mentalDetector/Quansheng_UV-K5_PCB_R51-V1.4_PCB_Reversing_Rev._0.9/Quansheng_UV-K5_PCB_R51-V1.4.kicad_sch

## KiCad design Quansheng_UV-K5_PCB_R51-V1.4.kicad_sch (2024-04-22)

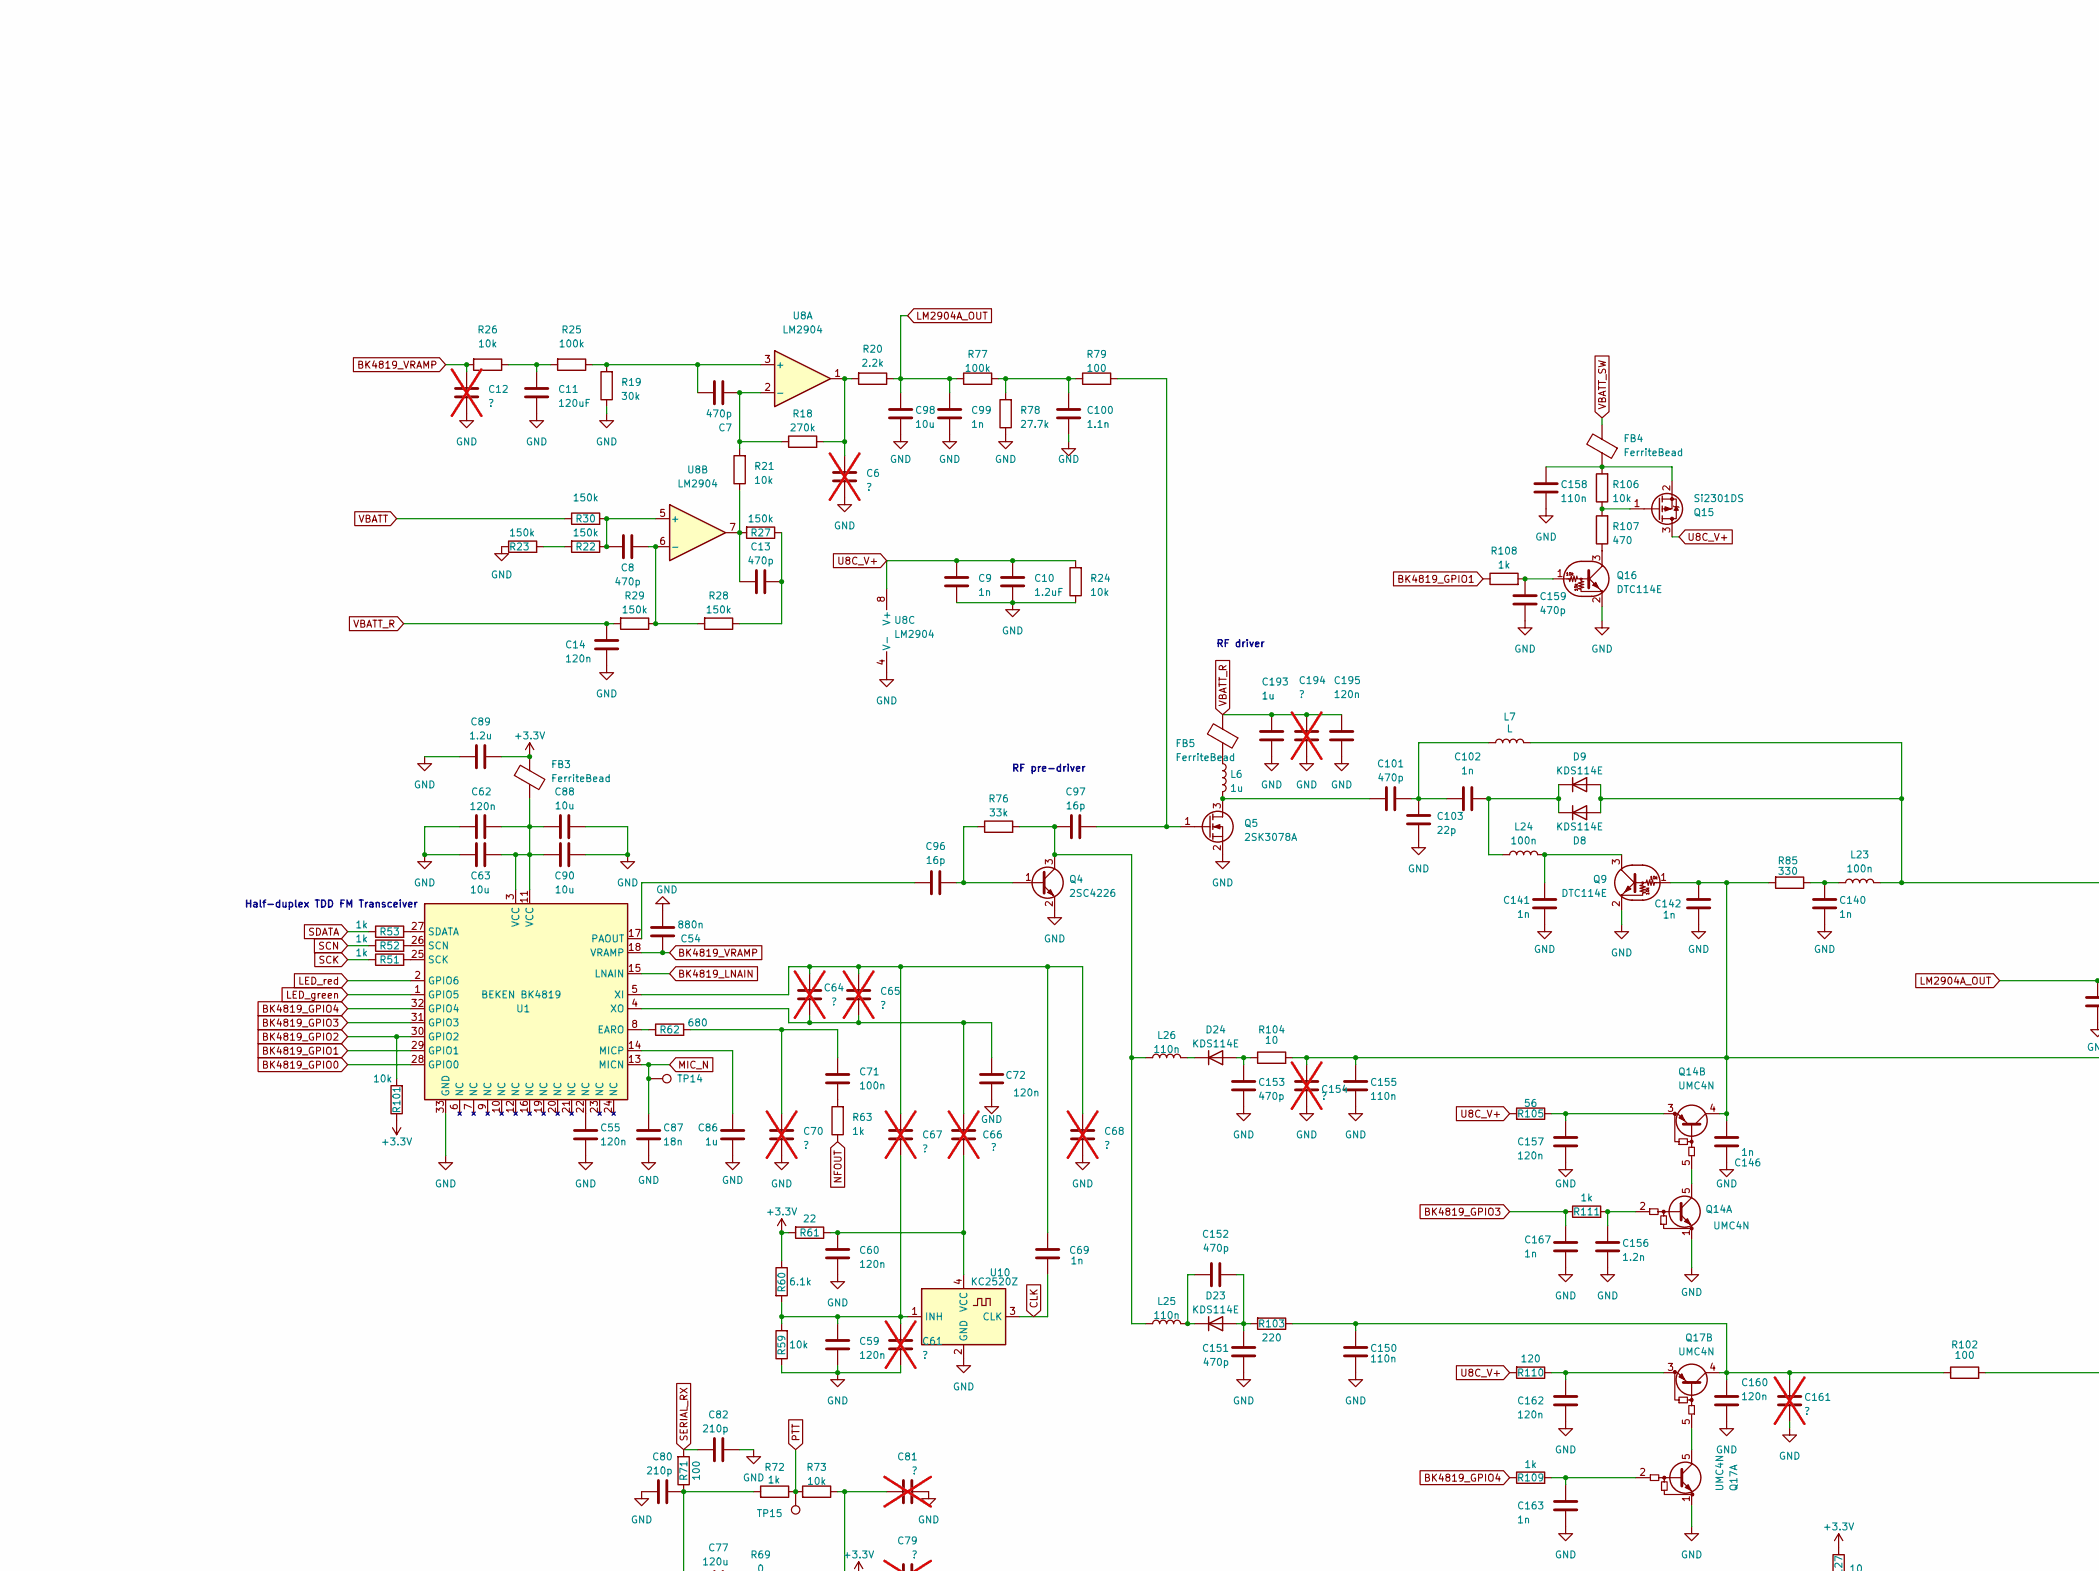
[picture p12: schematic Quansheng_UV-K5_PCB_R51-V1.4.kicad_sch, part in row 1, column 1]

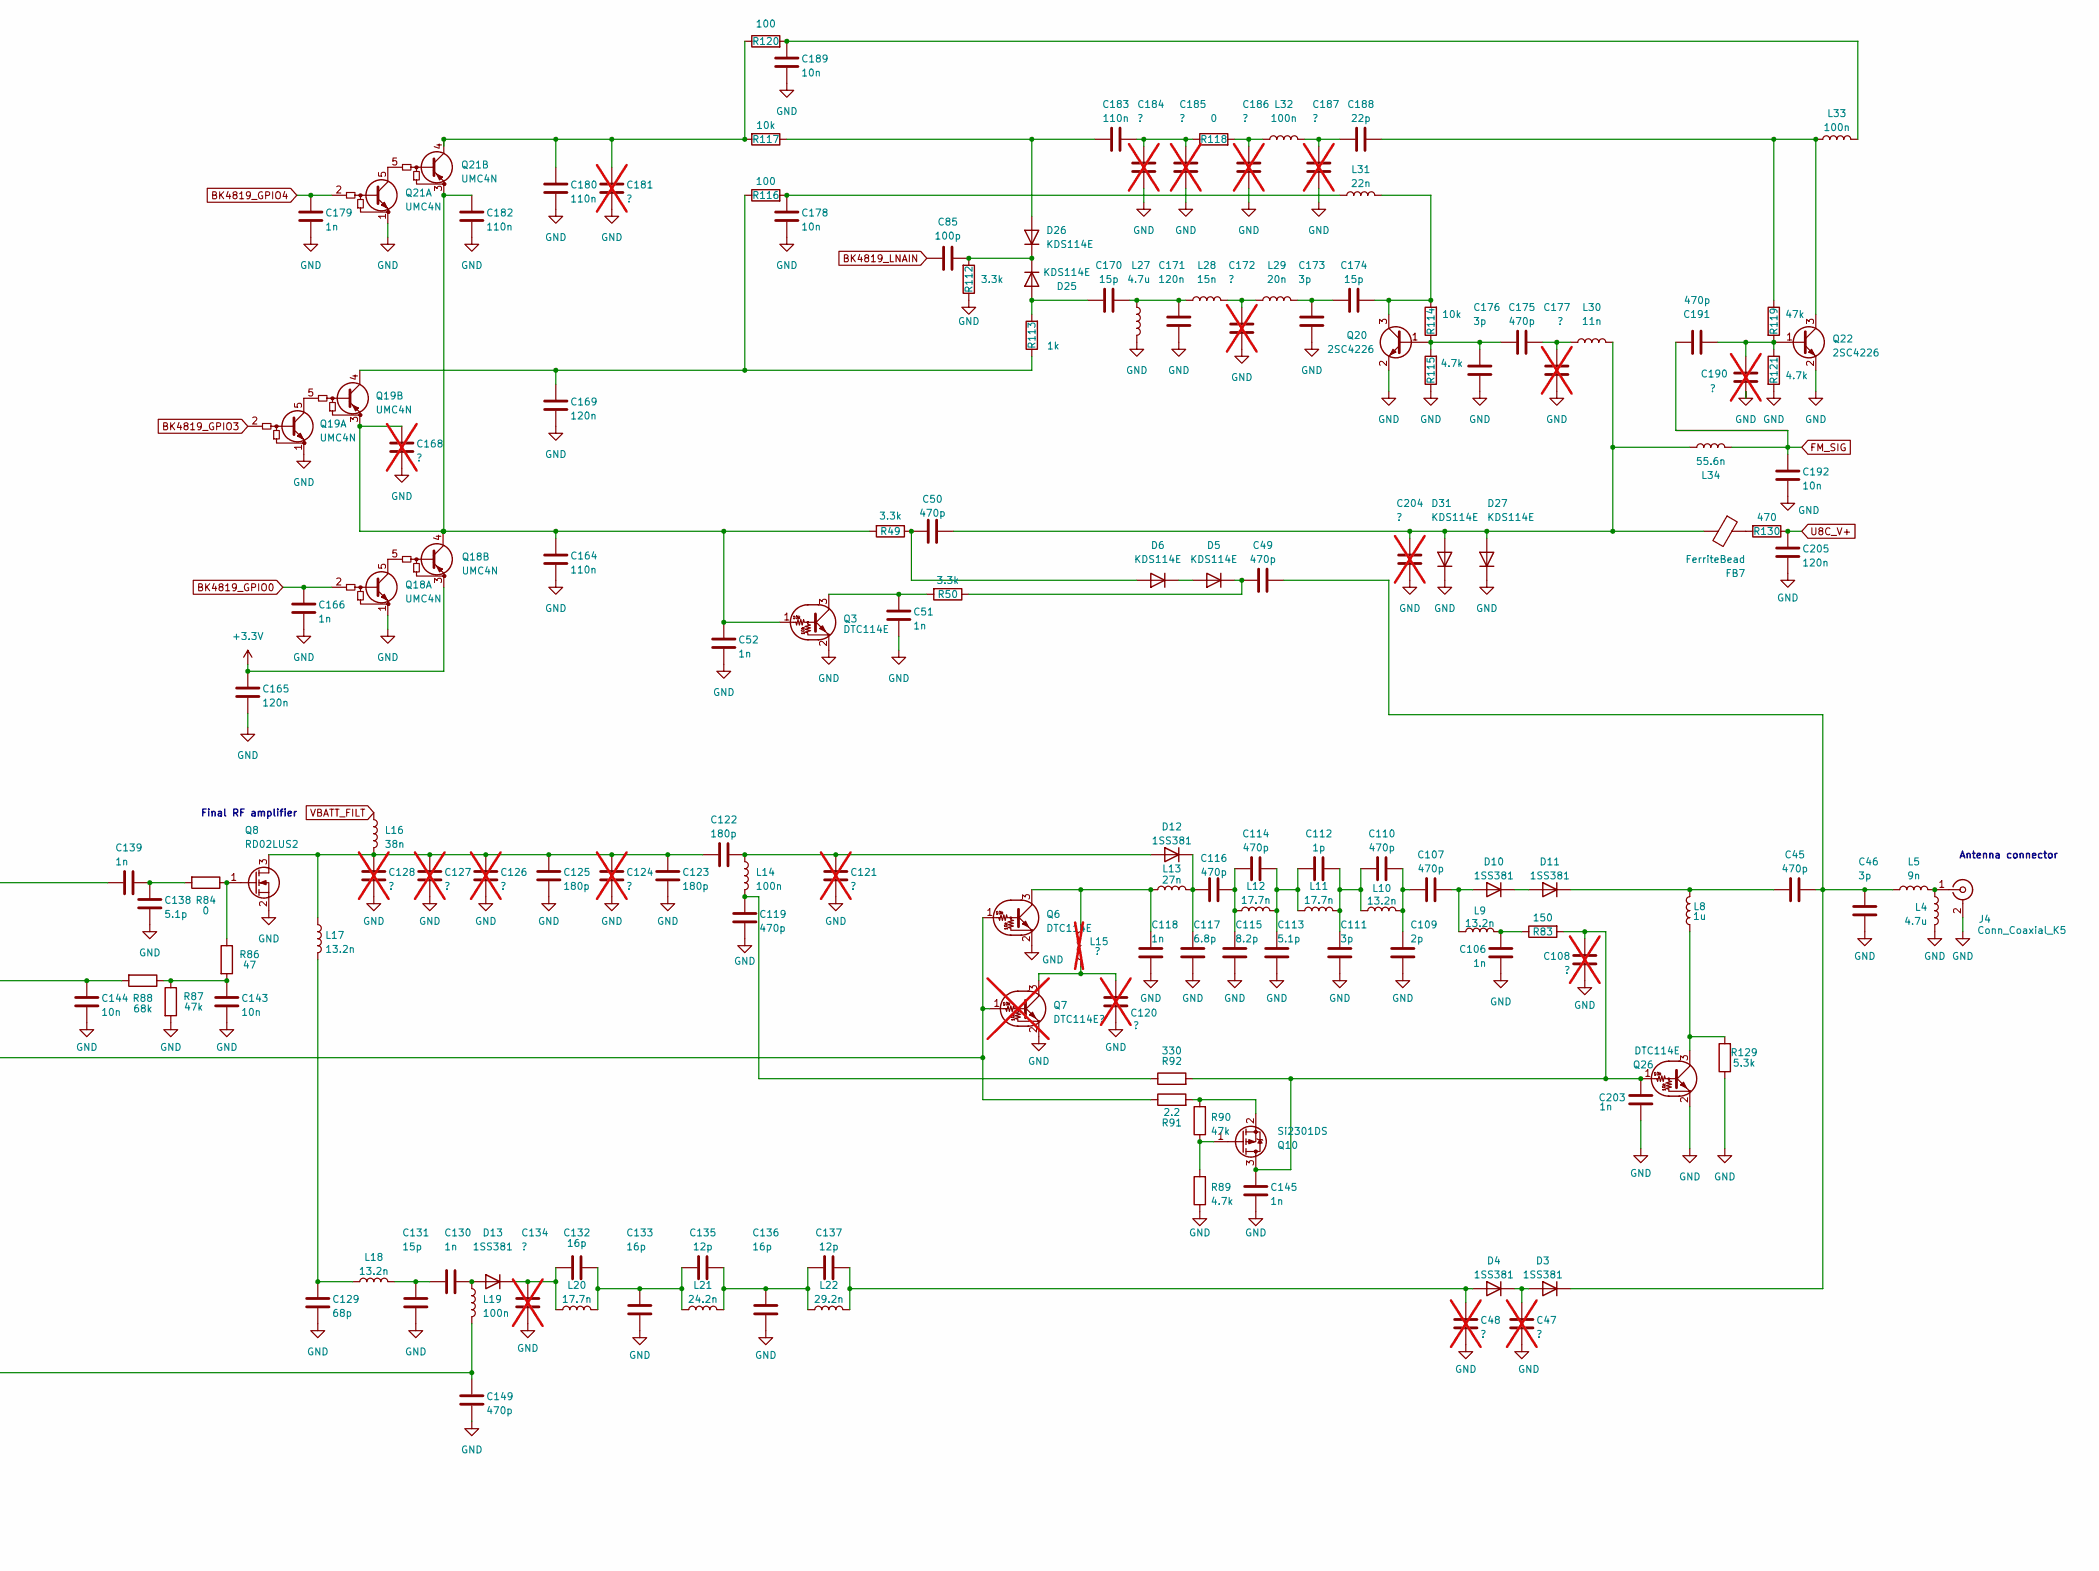
[picture p13: schematic Quansheng_UV-K5_PCB_R51-V1.4.kicad_sch, part in row 1, column 2]

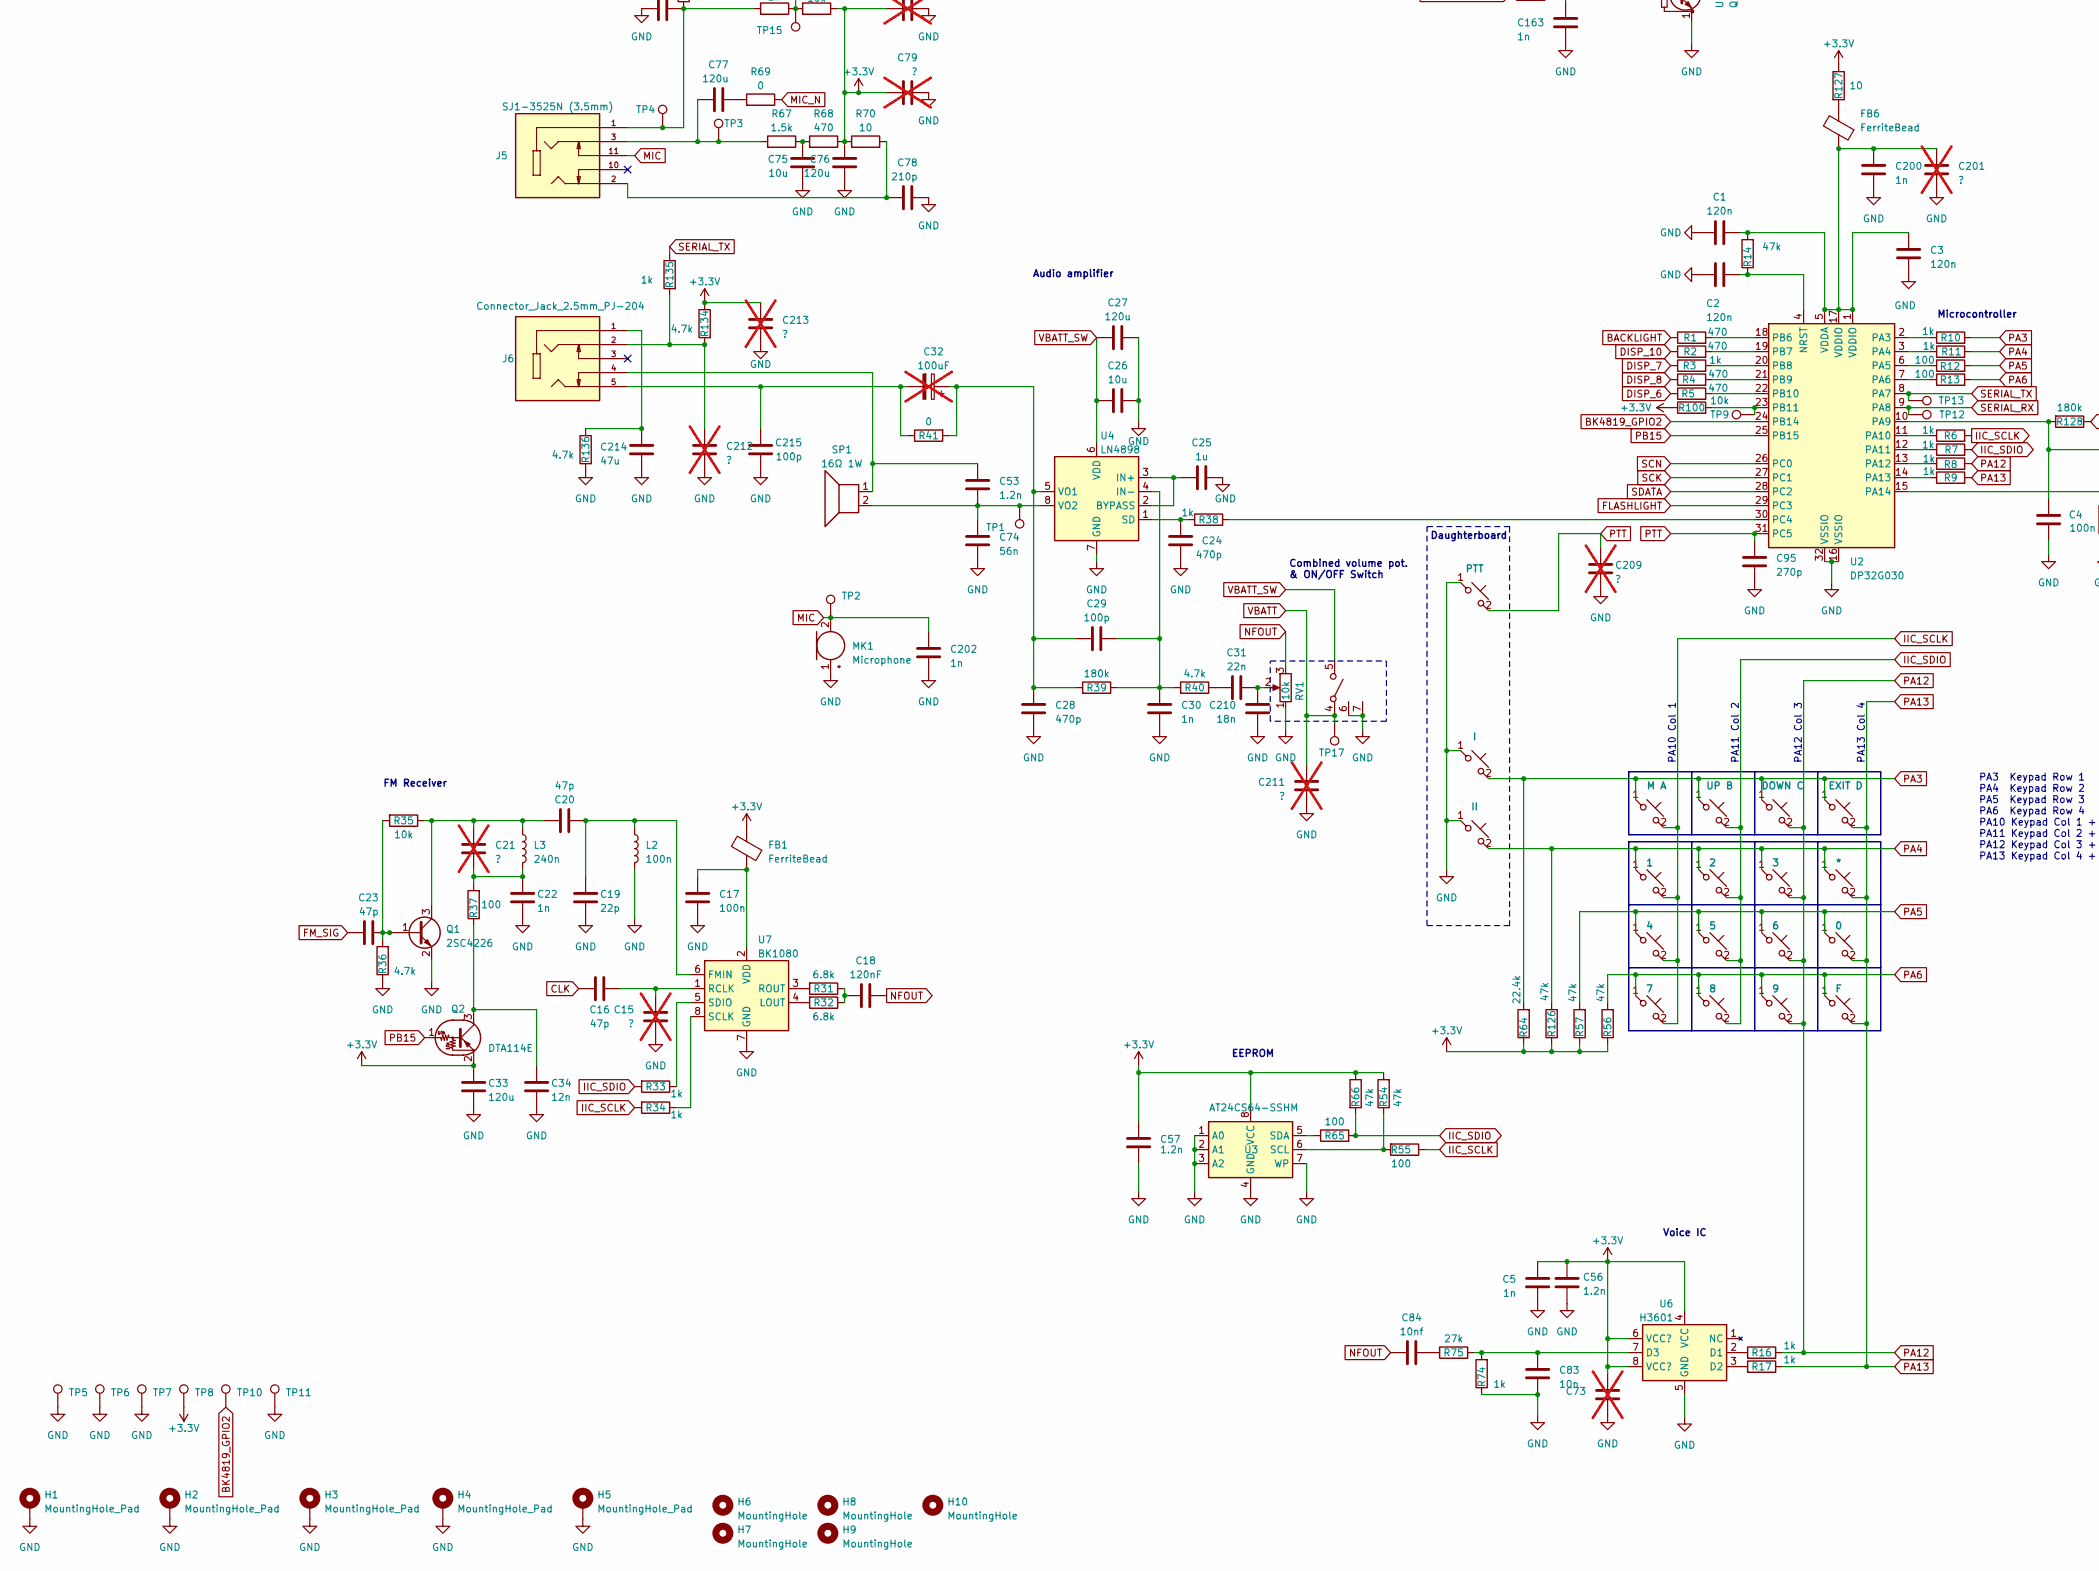
[picture p14: schematic Quansheng_UV-K5_PCB_R51-V1.4.kicad_sch, part in row 2, column 1]

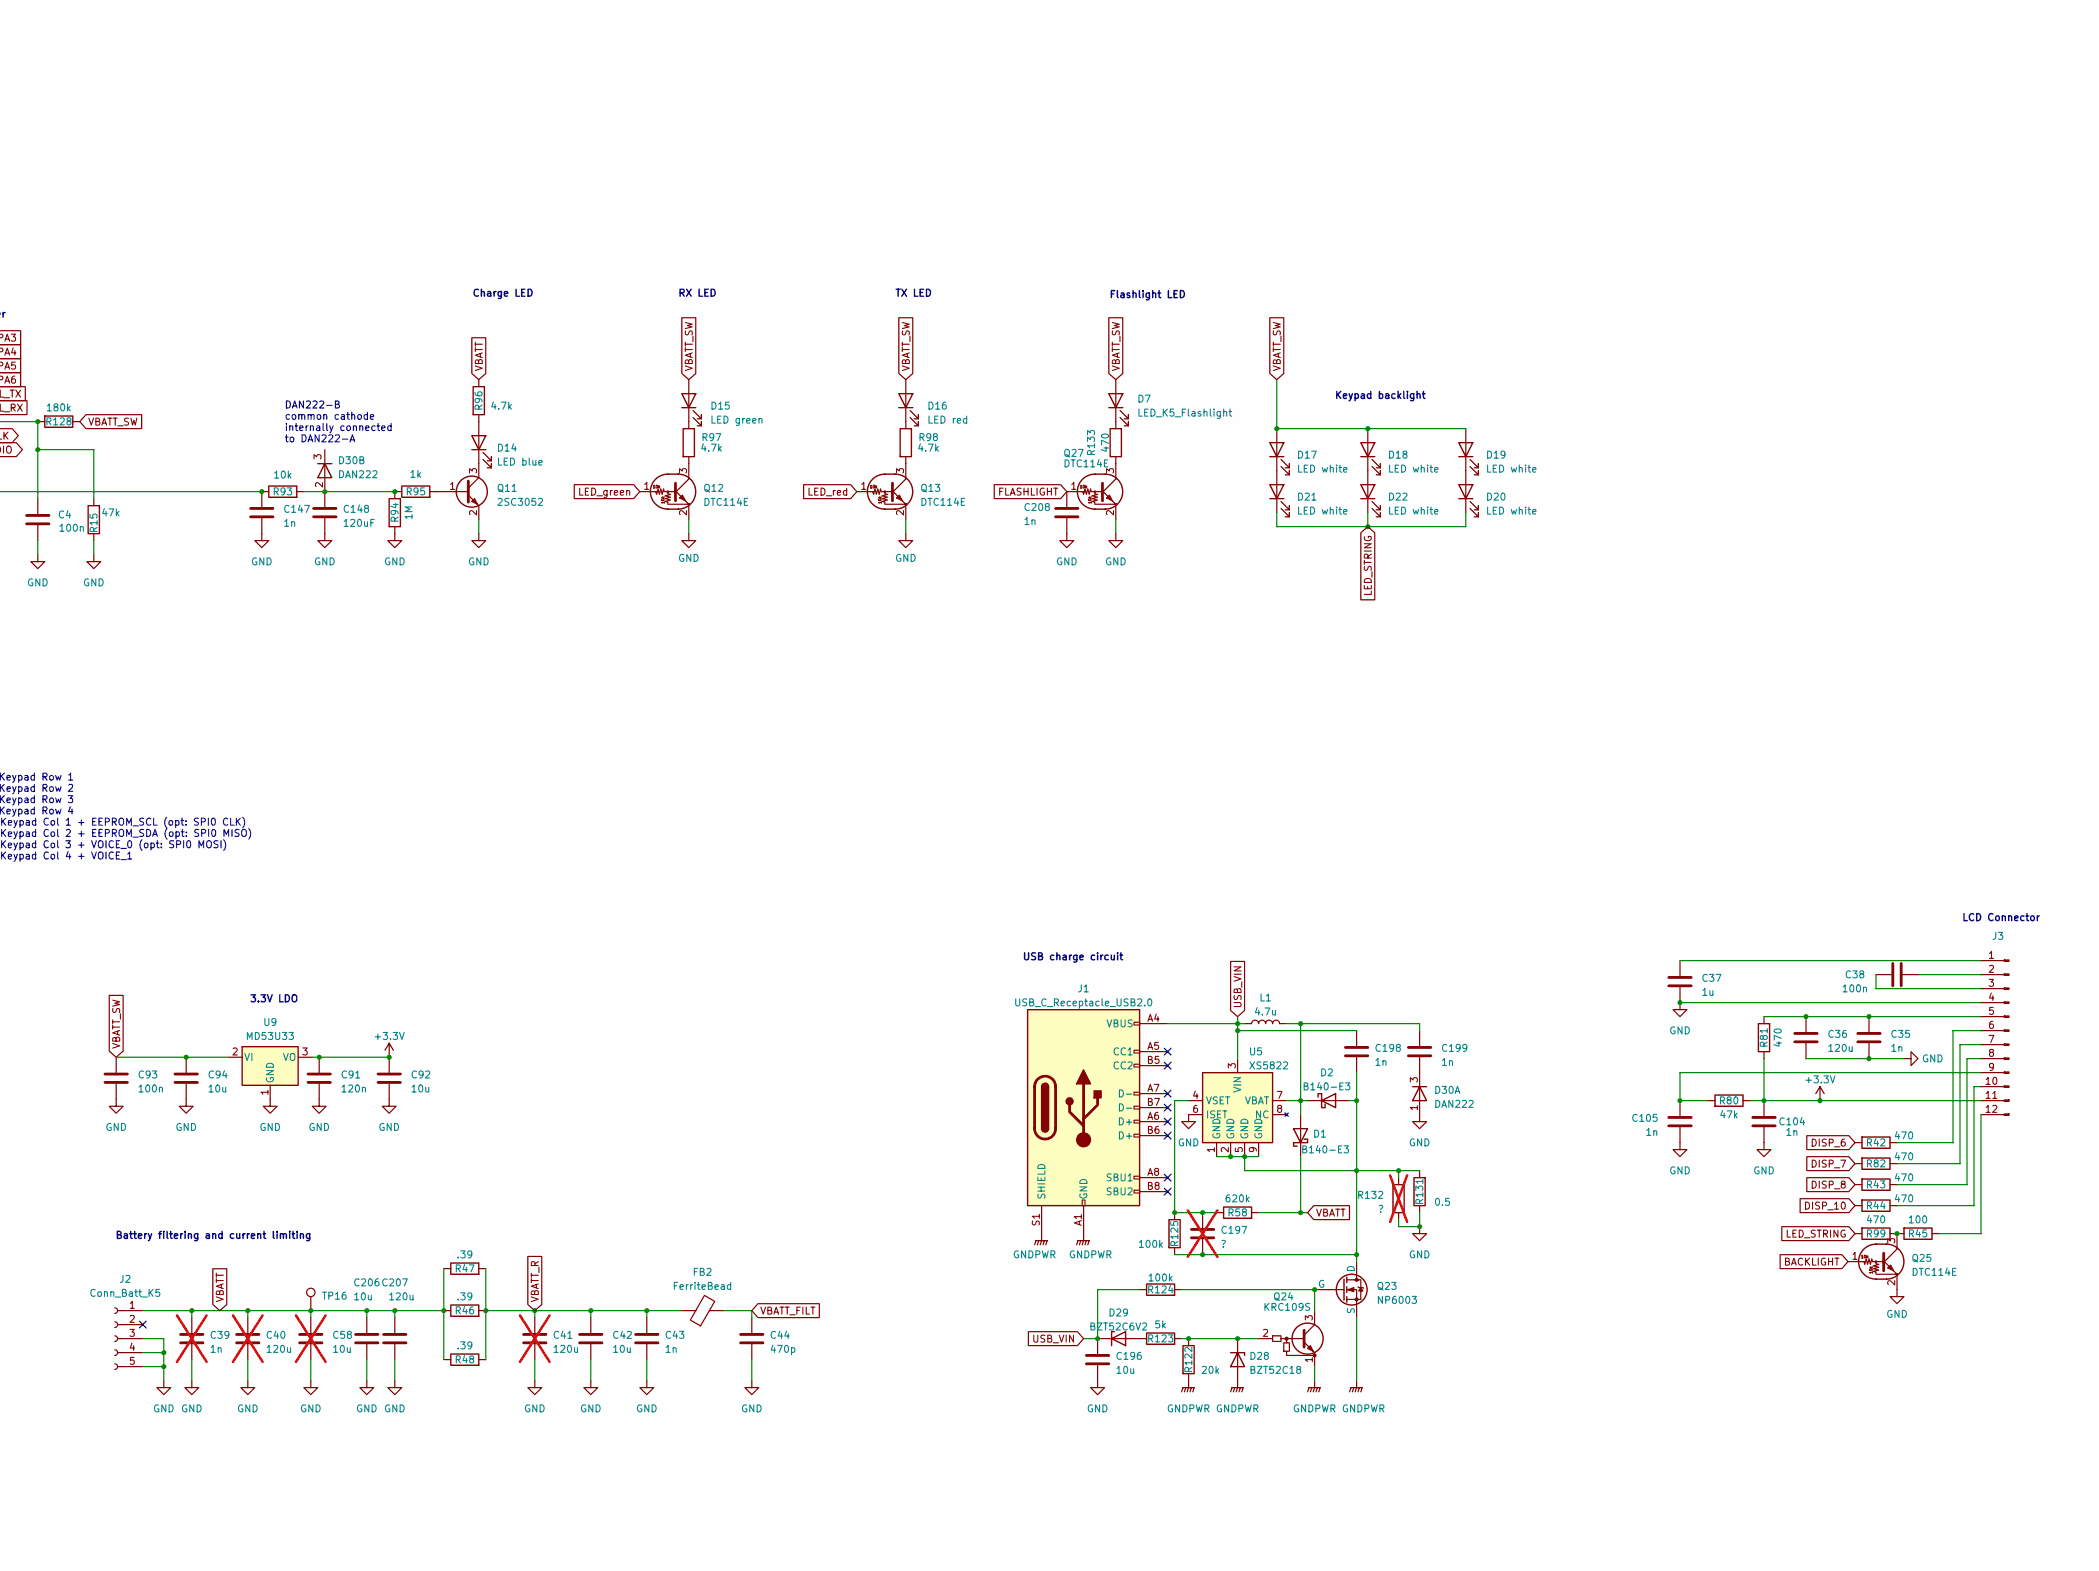
[picture p15: schematic Quansheng_UV-K5_PCB_R51-V1.4.kicad_sch, part in row 2, column 2]

Parts:
C1, C2, C3, C14, C55, C59, C60, C62, C72, C91, C157, C160, C162, C165, C169, C171, C195, C205: 120n; C_0402_1005Metric
C4, C17, C71, C93: 100n; C_0402_1005Metric
C5, C9, C22, C30, C35, C43, C51, C52, C69, C99, C104, C105, C106, C118, C140, C141, C142, C145, C146, C147, C163, C166, C167, C179, C198, C199, C200, C202, C203, C208: 1n; C_0402_1005Metric
C6, C12, C15, C21, C48, C64, C65, C66, C67, C68, C70, C73, C79, C81, C108, C120, C121, C168, C172, C177, C181, C185, C186, C187, C190, C194, C197, C209, C211, C212, C213: ?; C_0402_1005Metric; not fitted
C7, C8, C13, C24, C28, C44, C45, C49, C119, C151, C152, C153, C159, C175, C191: 470p; C_0402_1005Metric
C10: 1.2uF; C_0402_1005Metric
C11, C148: 120uF; C_0402_1005Metric
C16, C20, C23: 47p; C_0402_1005Metric
C18: 120nF; C_0402_1005Metric
C19, C188: 22p; C_0402_1005Metric
C25: 1u; C_0402_1005Metric
C26, C63, C75, C92, C98: 10u; C_0603_1608Metric
C27, C33, C36, C76, C77, C207: 120u; C_0402_1005Metric
C29, C215: 100p; C_0402_1005Metric
C31: 22n; C_0402_1005Metric
C32: 100uF; CP_EIA-6032-20_AVX-F; not fitted
C34: 12n; C_0402_1005Metric
C37, C86, C193: 1u; C_0603_1608Metric
C38: 100n; C_0603_1608Metric
C39: 1n; C_0402_1005Metric; not fitted
C40, C41: 120u; C_0805_2012Metric; not fitted
C42, C196, C206: 10u; C_0805_2012Metric
C46, C173, C176: 3p; C_0402_1005Metric
C47, C61, C124, C126, C127, C128, C134, C154, C161, C184, C201, C204: ?; C_0603_1608Metric; not fitted
C50, C101, C107, C110, C114, C116, C149: 470p; C_0603_1608Metric
C53, C56, C57, C156: 1.2n; C_0402_1005Metric
C54: 880n; C_0603_1608Metric
C58: 10u; C_0805_2012Metric; not fitted
C74: 56n; C_0402_1005Metric
C78, C80, C82: 210p; C_0402_1005Metric
C83, C143, C144, C178, C189, C192: 10n; C_0402_1005Metric
C84: 10nf; C_0402_1005Metric
C85: 100p; C_0603_1608Metric
C87, C210: 18n; C_0402_1005Metric
C88: 10u; C_0402_1005Metric_Pad0.74x0.62mm_HandSolder
C89: 1.2u; C_0402_1005Metric
C90: 10u; C_0402_1005Metric
C94: 10u; C_0603_1608Metric_Pad1.08x0.95mm_HandSolder
C95: 270p; C_0402_1005Metric
C96: 16p; C_0402_1005Metric
C97, C132, C133, C136: 16p; C_0603_1608Metric
C100: 1.1n; C_0402_1005Metric
C102, C130, C139: 1n; C_0603_1608Metric
C103: 22p; C_0603_1608Metric
C109: 2p; C_0603_1608Metric
C111: 3p; C_0603_1608Metric
C112: 1p; C_0603_1608Metric
C113: 5.1p; C_0603_1608Metric
C115: 8.2p; C_0603_1608Metric
C117: 6.8p; C_0603_1608Metric
C122, C123, C125: 180p; C_0603_1608Metric
C129: 68p; C_0603_1608Metric
C131: 15p; C_0603_1608Metric
C135, C137: 12p; C_0603_1608Metric
C138: 5.1p; C_0402_1005Metric
C150, C155, C158, C164, C180, C182, C183: 110n; C_0402_1005Metric
C170, C174: 15p; C_0402_1005Metric
C214: 47u; C_1206_3216Metric
D1, D2: B140-E3; D_SMA
D3, D4, D10, D11, D12, D13: 1SS381; D_SOD-323
D5, D6, D23, D24: KDS114E; D_SOD-323
D7: LED_K5_Flashlight; LED_D5.0mm_White_K5
D8, D9, D25, D26, D27, D31: KDS114E; D_SOD-523
D14: LED blue; LED_0603_1608Metric
D15: LED green; LED_0603_1608Metric
D16: LED red; LED_0603_1608Metric
D17, D18, D19, D20, D21, D22: LED white; LED_0603_1608Metric
D28: BZT52C18; D_SOD-123F
D29: BZT52C6V2; D_SOD-123F
D30: DAN222; SOT-323_SC-70
FB1: FerriteBead; R_0402_1005Metric
FB2, FB4, FB5, FB6: FerriteBead; R_0603_1608Metric
FB3: FerriteBead; R_0402_1005Metric_Pad0.72x0.64mm_HandSolder
FB7: FerriteBead; L_0603_1608Metric
H1, H2, H3, H4, H5: MountingHole_Pad; MountingHole_2.2mm_M2_Pad_TopBottom
H6, H7, H8, H9, H10: MountingHole; MountingHole_1.5mm
J1: USB_C_Receptacle_USB2.0; USB_C_Receptacle_Palconn_UTC16-G
J2: Conn_Batt_K5; Connector_Battery_3_pin
J3: Connector_K5_Display
J4: Conn_Coaxial_K5; Connector_K5_Horizontal
J5: SJ1-3525N (3.5mm); CUI_SJ1-3525N; PARTREV 1.05
J6: Connector_Jack_2.5mm_PJ-204
L1: 4.7u; L_Changjiang_FNR5045S
L2, L23, L24, L32, L33: 100n; L_0603_1608Metric
L3: 240n; L_0603_1608Metric
L4: 4.7u; L_0805_2012Metric
L5: 9n; L_Changjiang_FNR252010S
L6, L8: 1u; L_0603_1608Metric
L7: L; L_0603_1608Metric
L9, L10, L17, L18: 13.2n; L_Changjiang_FNR252010S
L11, L12, L20: 17.7n; L_Changjiang_FNR252010S
L13: 27n; L_1206_3216Metric
L14, L19: 100n; L_0805_2012Metric
L15: ?; L_0603_1608Metric; not fitted
L16: 38n; L_1206_3216Metric
L21: 24.2n; L_Changjiang_FNR252010S
L22: 29.2n; L_Changjiang_FNR252010S
L25, L26: 110n; L_0603_1608Metric
L27: 4.7u; L_0603_1608Metric
L28: 15n; L_0402_1005Metric
L29: 20n; L_0603_1608Metric
L30: 11n; L_Changjiang_FNR252010S
L31: 22n; L_0603_1608Metric
L34: 55.6n; L_0603_1608Metric
MK1: Microphone; Microphone 6x2.2mm
Q1, Q4, Q20, Q22: 2SC4226; SOT-323_SC-70
Q2: DTA114E; SOT-416
Q3, Q6, Q9, Q12, Q13, Q16, Q25, Q26, Q27: DTC114E; SOT-416
Q5: 2SK3078A; SOT-89-3
Q7: DTC114E?; SOT-416; not fitted
Q8: RD02LUS2; SOT-89-3
Q10, Q15: Si2301DS; SOT-23W
Q11: 2SC3052; SOT-416
Q14, Q17, Q18, Q19, Q21: UMC4N; SOT-353_SC-70-5
Q23: NP6003; SOT-23W
Q24: KRC109S; KRC109S_SOT-23W
R1, R2, R4, R5, R42, R43, R44, R68, R81, R82, R99, R107, R130, R133: 470; R_0402_1005Metric
R3, R6, R7, R8, R9, R10, R11, R16, R17, R33, R34, R38, R51, R52, R53, R63, R72, R74, R95, R108, R109, R111, R113, R135: 1k; R_0402_1005Metric
R12, R13, R37, R45, R55, R65, R71, R79, R116, R120: 100; R_0402_1005Metric
R14, R15, R54, R56, R57, R66, R80, R87, R90, R119, R126: 47k; R_0402_1005Metric
R18: 270k; R_0402_1005Metric
R19: 30k; R_0402_1005Metric
R20: 2.2k; R_0402_1005Metric
R21: 10k; R_0603_1608Metric
R22, R23, R27, R28, R29, R30: 150k; R_0402_1005Metric
R24, R26, R35, R59, R73, R93, R100, R101, R106, R114, R117: 10k; R_0402_1005Metric
R25, R77, R124, R125: 100k; R_0402_1005Metric
R31, R32: 6.8k; R_0402_1005Metric
R36, R40, R89, R96, R97, R98, R115, R121, R134, R136: 4.7k; R_0402_1005Metric
R39: 180k; R_0603_1608Metric
R41, R69, R84: 0; R_0603_1608Metric
R46, R47, R48: .39; R_1206_3216Metric
R49, R50, R112: 3.3k; R_0402_1005Metric
R58: 620k; R_0402_1005Metric
R60: 6.1k; R_0402_1005Metric
R61: 22; R_0402_1005Metric
R62: 680; R_0402_1005Metric
R64: 22.4k; R_0402_1005Metric
R67: 1.5k; R_0402_1005Metric
R70, R104, R127: 10; R_0402_1005Metric
R75: 27k; R_0402_1005Metric
R76: 33k; R_0402_1005Metric
R78: 27.7k; R_0402_1005Metric
R83: 150; R_0402_1005Metric
R85, R92: 330; R_0402_1005Metric
R86: 47; R_0402_1005Metric
R88: 68k; R_0402_1005Metric
R91: 2.2; R_0603_1608Metric
R94: 1M; R_0402_1005Metric
R102: 100; R_0603_1608Metric
R103: 220; R_0402_1005Metric
R105: 56; R_0603_1608Metric
R110: 120; R_0603_1608Metric
R118: 0; R_0402_1005Metric
R122: 20k; R_0402_1005Metric
R123: 5k; R_0402_1005Metric
R128: 180k; R_0402_1005Metric
R129: 5.3k; R_0402_1005Metric
R131: 0.5; R_1206_3216Metric
R132: ?; R_1206_3216Metric; not fitted
RV1: 10k; Potentiometer_Alps_RK097_Single_Horizontal_Switch
SP1: 16Ω 1W; Speaker_Pads
SW1: 1; SW_UV-K5_Button
SW2: 2; SW_UV-K5_Button
SW3: 3; SW_UV-K5_Button
SW4: 4; SW_UV-K5_Button
SW5: 5; SW_UV-K5_Button
SW6: 6; SW_UV-K5_Button
SW7: 7; SW_UV-K5_Button
SW8: 8; SW_UV-K5_Button
SW9: 9; SW_UV-K5_Button
SW10: 0; SW_UV-K5_Button
SW11: *; SW_UV-K5_Button
SW12: F; SW_UV-K5_Button
SW13: M A; SW_UV-K5_Button
SW14: UP B; SW_UV-K5_Button
SW15: DOWN C; SW_UV-K5_Button
SW16: EXIT D; SW_UV-K5_Button
SW17: PTT; SW_UV-K5_Button
SW18: I; SW_UV-K5_Button
SW19: II; SW_UV-K5_Button
TP1, TP2, TP3, TP4, TP5, TP6, TP7, TP8, TP9, TP10, TP11, TP12, TP13, TP14, TP15, TP16, TP17: TestPoint; TestPoint_Pad_D1.4mm
U1: BEKEN BK4819; BK4819_QFN-32-1EP_4x4mm_P0.4mm_EP2.9x2.9mm
U2: DP32G030; LQFP-32_7x7mm_P0.8mm
U3: AT24CS64-SSHM; SO-8_3.9x4.9mm_P1.27mm
U4: LN4898
U5: XS5822; HTSOP-8-1EP_3.9x4.9mm_P1.27mm_EP2.4x3.2mm
U6: H3601; SSOP-8_3.9x5.05mm_P1.27mm
U7: BK1080; HTSOP-8-1EP_3.9x4.9mm_P1.27mm
U8: LM2904; TSSOP-8_4.4x3mm_P0.65mm
U9: MD53U33; SOT-89-3
U10: KC2520Z; Oscillator_SMD_Kyocera_KC2520Z-4Pin_2.5x2.0mm

Connections:
+3.3V: C5.1, C33.1, C56.2, C57.1, C73.1, C76.1, C79.1, C81.1, C89.2, C91.1, C92.1, C104.1, C165.1, C213.1, FB1.1, FB3.1, J3.11, Q2.2 (E), Q18.3 (E2), R54.2, R56.1, R57.1, R60.1, R61.2, R64.1, R66.1, R68.1, R70.2, R73.1, R80.1, R81.1, R100.1, R101.1, R126.2, R127.1, R134.1, TP8.1, U3.8 (VCC), U6.4 (VCC), U6.6 (VCC?), U6.8 (VCC?), U9.3 (VO)
BACKLIGHT: Q25.1 (B), R1.1
BK4819_GPIO0: C166.1, Q18.2 (B1), U1.28 (GPIO0)
BK4819_GPIO1: R108.1, U1.29 (GPIO1)
BK4819_GPIO2: R101.2, TP10.1, U1.30 (GPIO2), U2.24 (PB14)
BK4819_GPIO3: C167.1, Q19.2 (B1), R111.1, U1.31 (GPIO3)
BK4819_GPIO4: C179.1, Q21.2 (B1), R109.1, U1.32 (GPIO4)
BK4819_LNAIN: C85.1, U1.15 (LNAIN)
BK4819_VRAMP: C12.1, C54.1, R26.2, U1.18 (VRAMP)
CLK: C16.1, C69.2, U10.3 (CLK)
DISP_6: R5.1, R42.2
DISP_7: R3.1, R82.2
DISP_8: R4.1, R43.2
DISP_10: R2.1, R44.2
FLASHLIGHT: C208.1, Q27.1 (B), U2.29 (PC3)
FM_SIG: C23.1, C191.1, C192.1, L34.1
GND: C1.1, C2.2, C3.2, C4.2, C5.2, C6.2, C9.2, C10.2, C11.2, C12.2, C14.2, C15.2, C17.2, C19.2, C22.2, C24.2, C25.1, C26.1, C27.1, C28.2, C30.2, C33.2, C34.2, C35.2, C36.2, C37.2, C39.2, C40.2, C41.2, C42.2, C43.2, C44.2, C46.2, C47.2, C48.2, C51.2, C52.2, C54.2, C55.2, C56.1, C57.2, C58.2, C59.2, C60.2, C61.2, C62.1, C63.1, C68.2, C70.2, C72.2, C73.2, C74.2, C75.2, C76.2, C78.2, C79.2, C80.1, C81.2, C82.2, C83.2, C86.2, C87.2, C88.2, C89.1, C90.2, C91.2, C92.2, C93.2, C94.2, C95.2, C98.2, C99.2, C100.2, C103.1, C104.2, C105.2, C106.2, C108.2, C109.2, C111.2, C113.2, C115.2, C117.2, C118.2, C119.2, C120.2, C121.2, C123.2, C124.2, C125.2, C126.2, C127.2, C128.2, C129.2, C131.2, C133.2, C134.2, C136.2, C138.2, C140.2, C141.2, C142.2, C143.2, C144.2, C145.2, C146.2, C147.2, C148.1, C149.2, C150.2, C151.2, C153.2, C154.2, C155.2, C156.2, C157.2, C158.2, C159.2, C160.2, C161.2, C162.2, C163.2, C164.2, C165.2, C166.2, C167.2, C168.2, C169.2, C171.2, C172.2, C173.2, C176.2, C177.2, C178.2, C179.2, C180.2, C181.2, C182.2, C184.1, C185.1, C186.1, C187.1, C189.2, C190.1, C192.2, C193.1, C194.1, C195.1, C196.2, C200.2, C201.2, C202.2, C203.2, C204.2, C205.2, C206.2, C207.2, C208.2, C209.2, C210.1, C211.1, C212.2, C213.2, C214.1, C215.2, D27.1 (K), D30.1 (A), D31.1 (K), H1.1, H2.1, H3.1, H4.1, H5.1, J2.3, J2.4, J2.5, J3.4, J4.2 (Ext), L2.2, L4.1, L27.1, MK1.1 (+), Q1.2 (E), Q3.2 (E), Q4.2 (E), Q5.2 (S), Q6.2 (E), Q7.2 (E), Q8.2 (S), Q9.2 (E), Q11.2 (E), Q12.2 (E), Q13.2 (E), Q14.1 (E1), Q16.2 (E), Q17.1 (E1), Q18.1 (E1), Q19.1 (E1), Q20.2 (E), Q21.1 (E1), Q22.2 (E), Q25.2 (E), Q26.2 (E), Q27.2 (E), R15.1, R19.1, R23.1, R24.1, R36.1, R59.1, R74.1, R78.1, R87.2, R89.1, R94.2, R112.1, R115.1, R121.2, R129.1, R131.1, R132.1, R136.2, RV1.1, RV1.6, RV1.7, SW17.1, SW18.1, SW19.1, TP5.1, TP6.1, TP7.1, TP11.1, U1.33 (GND), U2.16 (VSSIO), U2.32 (VSSIO), U3.1 (A0), U3.2 (A1), U3.3 (A2), U3.4 (GND), U3.7 (WP), U4.7 (GND), U5.6 (ISET), U6.5 (GND), U7.7 (GND), U8.4 (V-), U9.1 (GND), U10.2 (GND)
GNDPWR: D28.2 (A), J1.A1 (GND), J1.A12 (GND), J1.B1 (GND), J1.B12 (GND), J1.S1 (SHIELD), Q23.2 (S), Q24.1 (E), R122.2
IIC_SCLK: R6.2, R34.2, R55.1, SW1.2, SW4.2, SW7.2, SW13.2
IIC_SDIO: R7.2, R33.2, R65.2, R66.2, SW2.2, SW5.2, SW8.2, SW14.2
LED_STRING: D20.1 (K), D21.1 (K), D22.1 (K), R99.2
LED_green: Q12.1 (B), U1.1 (GPIO5)
LED_red: Q13.1 (B), U1.2 (GPIO6)
LM2904A_OUT: C98.1, C99.1, C144.1, R20.1, R77.1, R88.2
MIC: C202.1, J5.11, MK1.2 (-), TP2.1
MIC_N: C87.1, R69.1, TP14.1, U1.13 (MICN)
NFOUT: C18.2, C84.2, R63.1, RV1.3
unnamed: C1.2, C3.1, C200.1, C201.1, FB6.1, R14.2, U2.1 (VDDIO), U2.5 (VDDA), U2.17 (VDDIO)
unnamed: C2.1, R14.1, U2.4 (NRST)
unnamed: C4.1, R15.2, R128.2, U2.10 (PA9)
unnamed: C6.1, R18.2, R20.2, U8.1
unnamed: C7.1, R19.2, R25.1, U8.3 (+)
unnamed: C7.2, R18.1, R21.2, U8.2 (-)
unnamed: C8.1, R22.1, R30.2, U8.5 (+)
unnamed: C8.2, R28.2, R29.1, U8.6 (-)
unnamed: C11.1, R25.2, R26.1
unnamed: C13.1, R27.1, R28.1
unnamed: C13.2, R21.1, R27.2, U8.7
unnamed: C15.1, C16.2, U7.1 (RCLK)
unnamed: C17.1, FB1.2, U7.2 (VDD)
unnamed: C18.1, R31.1, R32.1
unnamed: C19.1, C20.2, L2.1, U7.6 (FMIN)
unnamed: C20.1, C21.1, L3.1, Q1.3 (C), R35.1
unnamed: C21.2, C22.1, L3.2, R37.2
unnamed: C23.2, Q1.1 (B), R35.2, R36.2
unnamed: C24.1, R38.2, U4.1 (SD)
unnamed: C25.2, U4.2 (BYPASS), U4.3 (IN+)
unnamed: C28.1, C29.2, C32.1, R39.2, R41.2, U4.5 (VO1)
unnamed: C29.1, C30.1, R39.1, R40.2, U4.4 (IN-)
unnamed: C31.2, R40.1
unnamed: C34.1, Q2.3 (C), R37.1
unnamed: C35.1, C36.1, J3.5, R81.2
unnamed: C37.1, J3.1
unnamed: C38.1, J3.3
unnamed: C38.2, J3.2
unnamed: C45.1, D11.1 (K), L8.2
unnamed: C45.2, C46.1, C49.2, D3.1 (K), L5.1
unnamed: C47.1, D3.2 (A), D4.1 (K)
unnamed: C49.1, D5.1 (K), R50.1
unnamed: C50.2, D6.2 (A), R49.1
unnamed: C51.1, Q3.3 (C), R50.2
unnamed: C53.1, J6.4, SP1.1
unnamed: C53.2, C74.1, SP1.2, TP1.1, U4.8 (VO2)
unnamed: C55.1, U1.22 (NC)
unnamed: C59.1, C61.1, C67.2, R59.2, R60.2, U10.1 (INH)
unnamed: C60.1, C66.2, R61.1, U10.4 (VCC)
unnamed: C62.2, C63.2, C88.1, C90.1, FB3.2, U1.3 (VCC), U1.11 (VCC)
unnamed: C64.1, C65.1, C67.1, C68.1, C69.1, U1.5 (XI)
unnamed: C64.2, C65.2, C66.1, C72.1, U1.4 (XO)
unnamed: C70.1, C71.2, R62.2
unnamed: C71.1, R63.2
unnamed: C75.1, R67.1, R68.2
unnamed: C77.1, J5.3, R67.2, TP3.1
unnamed: C77.2, R69.2
unnamed: C78.1, J5.2, R70.1
unnamed: C80.2, J5.1, R71.1, R72.2, TP4.1
unnamed: C83.1, R74.2, R75.2, U6.7 (D3)
unnamed: C84.1, R75.1
unnamed: C85.2, D25.1 (K), D26.1 (K), R112.2
unnamed: C86.1, U1.14 (MICP)
unnamed: C96.1, U1.17 (PAOUT)
unnamed: C96.2, Q4.1 (B), R76.1
unnamed: C97.1, L25.1, L26.1, Q4.3 (C), R76.2
unnamed: C97.2, Q5.1 (G), R79.2
unnamed: C100.1, R77.2, R78.2, R79.1
unnamed: C101.1, L6.2, Q5.3 (D)
unnamed: C101.2, C102.1, C103.2, L7.1
unnamed: C102.2, D8.1 (K), D9.1 (K), L24.1
unnamed: C105.1, J3.9, R80.2
unnamed: C106.1, L9.1, R83.1
unnamed: C107.1, C109.1, C110.2, L10.2
unnamed: C107.2, D10.2 (A), L9.2
unnamed: C108.1, C145.1, C203.1, Q10.3 (D), Q26.1 (B), R83.2, R92.2
unnamed: C110.1, C111.1, C112.2, L10.1, L11.2
unnamed: C112.1, C113.1, C114.2, L11.1, L12.2
unnamed: C114.1, C115.1, C116.2, L12.1
unnamed: C116.1, C117.1, D12.1 (K), L13.2
unnamed: C118.1, L13.1, L15.2, Q6.3 (C)
unnamed: C119.1, L14.2, R92.1
unnamed: C120.1, L15.1, Q7.3 (C)
unnamed: C121.1, C122.1, D12.2 (A), L14.1
unnamed: C122.2, C123.1, C124.1, C125.1, C126.1, C127.1, C128.1, L16.2, L17.1, Q8.3 (D)
unnamed: C129.1, L17.2, L18.1
unnamed: C130.1, D13.2 (A), L19.1
unnamed: C130.2, C131.1, L18.2
unnamed: C132.1, C134.1, D13.1 (K), L20.1
unnamed: C132.2, C133.1, C135.1, L20.2, L21.1
unnamed: C135.2, C136.1, C137.1, L21.2, L22.1
unnamed: C48.1, C137.2, D4.2 (A), L22.2
unnamed: C138.1, C139.1, R84.2
unnamed: C139.2, D8.2 (A), D9.2 (A), L7.2, L23.2
unnamed: C140.1, L23.1, R85.1
unnamed: C141.1, L24.2, Q9.3 (C)
unnamed: C142.1, C146.1, C154.1, C155.1, Q6.1 (B), Q7.1 (B), Q9.1 (B), Q14.4 (C2), R85.2, R91.1, R104.2
unnamed: C143.1, R86.2, R87.1, R88.1
unnamed: C147.1, R93.1, U2.15 (PA14)
unnamed: C148.2, D30.2 (A), R93.2, R94.1, R95.1
unnamed: C149.1, L19.2, R102.2
unnamed: C150.1, C160.1, C161.1, Q17.4 (C2), R102.1, R103.1
unnamed: C151.1, C152.2, D23.2 (A), R103.2
unnamed: C152.1, D23.1 (K), L25.2
unnamed: C153.1, D24.2 (A), R104.1
unnamed: C156.1, Q14.2 (B1), R111.2
unnamed: C157.1, Q14.3 (E2), R105.1
unnamed: C158.1, FB4.1, Q15.2 (S), R106.2
unnamed: C159.1, Q16.1 (B), R108.2
unnamed: C162.1, Q17.3 (E2), R110.1
unnamed: C163.1, Q17.2 (B1), R109.2
unnamed: C52.1, C164.1, C168.1, C182.1, Q3.1 (B), Q18.4 (C2), Q19.3 (E2), Q21.3 (E2), R49.2
unnamed: C169.1, Q19.4 (C2), R113.1, R116.1
unnamed: C170.1, D25.2 (A), R113.2
unnamed: C170.2, C171.1, L27.2, L28.1
unnamed: C172.1, L28.2, L29.1
unnamed: C173.1, C174.1, L29.2
unnamed: C174.2, L31.2, Q20.3 (C), R114.2
unnamed: C175.1, C176.1, Q20.1 (B), R114.1, R115.2
unnamed: C175.2, C177.1, L30.1
unnamed: C178.1, L31.1, R116.2
unnamed: C180.1, C181.1, Q21.4 (C2), R117.2, R120.1
unnamed: C183.1, D26.2 (A), R117.1
unnamed: C183.2, C184.2, C185.2, R118.1
unnamed: C186.2, L32.1, R118.2
unnamed: C187.2, C188.1, L32.2
unnamed: C188.2, L33.1, Q22.3 (C), R119.1
unnamed: C189.1, L33.2, R120.2
unnamed: C190.2, C191.2, Q22.1 (B), R119.2, R121.1
unnamed: C197.1, R58.1, R125.1, U5.4 (VSET)
unnamed: C197.2, C198.2, D2.2 (A), Q23.3 (D), R125.2, R131.2, R132.2, U5.1 (GND), U5.2 (GND), U5.5 (GND), U5.9 (GND)
unnamed: C199.1, D1.2 (A), D2.1 (K), L1.2, U5.7 (VBAT)
unnamed: C199.2, D30.3 (K)
unnamed: C50.1, C204.1, D27.2 (A), D31.2 (A), FB7.2, L30.2, L34.2
unnamed: C31.1, C210.2, RV1.2
unnamed: C212.1, J6.2, R134.2, R135.2
unnamed: C214.2, J6.1, R136.1
unnamed: C32.2, C215.1, J6.5, R41.1
unnamed: D5.2 (A), D6.1 (K)
unnamed: D7.1 (K), R133.2
unnamed: D10.1 (K), D11.2 (A)
unnamed: D14.1 (K), Q11.3 (C)
unnamed: D14.2 (A), R96.2
unnamed: D15.1 (K), R97.1
unnamed: D16.1 (K), R98.1
unnamed: D17.1 (K), D21.2 (A)
unnamed: D18.1 (K), D22.2 (A)
unnamed: D19.1 (K), D20.2 (A)
unnamed: D24.1 (K), L26.2
unnamed: D28.1 (K), Q24.2 (B), R122.1, R123.2
unnamed: D29.2 (A), R123.1
unnamed: FB5.1, L6.1
unnamed: FB6.2, R127.2
unnamed: FB7.1, R130.2
unnamed: J3.6, R42.1
unnamed: J3.7, R82.1
unnamed: J3.8, R43.1
unnamed: J3.10, R44.1
unnamed: J3.12 (Pin_11), R45.1
unnamed: J4.1 (In), L4.2, L5.2
unnamed: L8.1, Q26.3 (C), R129.2
unnamed: Q8.1 (G), R84.1, R86.1
unnamed: Q10.1 (G), R89.2, R90.1
unnamed: Q10.2 (S), R90.2, R91.2
unnamed: Q11.1 (B), R95.2
unnamed: Q12.3 (C), R97.2
unnamed: Q13.3 (C), R98.2
unnamed: Q15.1 (G), R106.1, R107.2
unnamed: Q16.3 (C), R107.1
unnamed: Q23.1 (G), Q24.3 (C), R124.2
unnamed: Q25.3 (C), R45.2, R99.1
unnamed: Q27.3 (C), R133.1
unnamed: R1.2, U2.18 (PB6)
unnamed: R2.2, U2.19 (PB7)
unnamed: R3.2, U2.20 (PB8)
unnamed: R4.2, U2.21 (PB9)
unnamed: R5.2, U2.22 (PB10)
unnamed: R6.1, U2.11 (PA10)
unnamed: R7.1, U2.12 (PA11)
unnamed: R8.1, U2.13 (PA12)
unnamed: R9.1, U2.14 (PA13)
unnamed: R10.1, U2.2 (PA3)
unnamed: R11.1, U2.3 (PA4)
unnamed: R12.1, U2.6 (PA5)
unnamed: R13.1, U2.7 (PA6)
unnamed: R16.2, U6.2 (D1)
unnamed: R17.2, U6.3 (D2)
unnamed: R22.2, R23.2
unnamed: R31.2, U7.3 (ROUT)
unnamed: R32.2, U7.4 (LOUT)
unnamed: R33.1, U7.5 (SDIO)
unnamed: R34.1, U7.8 (SCLK)
unnamed: R38.1, U2.30 (PC4)
unnamed: R51.2, U1.25 (SCK)
unnamed: R52.2, U1.26 (SCN)
unnamed: R53.2, U1.27 (SDATA)
unnamed: R54.1, R55.2, U3.6 (SCL)
unnamed: R62.1, U1.8 (EARO)
unnamed: R65.1, U3.5 (SDA)
unnamed: R100.2, TP9.1, U2.23 (PB11)
PA3: R10.2, R64.2, SW13.1, SW14.1, SW15.1, SW16.1, SW18.2
PA4: R11.2, R126.1, SW1.1, SW2.1, SW3.1, SW11.1, SW19.2
PA5: R12.2, R57.2, SW4.1, SW5.1, SW6.1, SW10.1
PA6: R13.2, R56.2, SW7.1, SW8.1, SW9.1, SW12.1
PA12: R8.2, R16.1, SW3.2, SW6.2, SW9.2, SW15.2
PA13: R9.2, R17.1, SW10.2, SW11.2, SW12.2, SW16.2
PB15: Q2.1 (B), U2.25 (PB15)
PTT: C95.1, C209.1, R72.1, R73.2, SW17.2, TP15.1, U2.31 (PC5)
SCK: R51.1, U2.27 (PC1)
SCN: R52.1, U2.26 (PC0)
SDATA: R53.1, U2.28 (PC2)
SERIAL_RX: C82.1, R71.2, TP12.1, U2.9 (PA8)
SERIAL_TX: R135.1, TP13.1, U2.8 (PA7)
U8C_V+: C9.1, C10.1, C205.1, Q15.3 (D), R24.2, R105.2, R110.2, R130.1, U8.8 (V+)
USB_VIN: C196.1, C198.1, D29.1 (K), J1.A4 (VBUS), J1.A9 (VBUS), J1.B4 (VBUS), J1.B9 (VBUS), L1.1, R124.1, U5.3 (VIN)
VBATT: C39.1, C40.1, C58.1, C206.1, C207.1, C211.2, D1.1 (K), J2.1, R30.1, R46.1, R47.1, R48.1, R58.2, R96.1, RV1.4, TP16.1, TP17.1
VBATT_FILT: C44.1, FB2.2, L16.1
VBATT_R: C14.1, C41.1, C42.1, C43.1, C193.2, C194.2, C195.2, FB2.1, FB5.2, R29.2, R46.2, R47.2, R48.2
VBATT_SW: C26.2, C27.2, C93.1, C94.1, D7.2 (A), D15.2 (A), D16.2 (A), D17.2 (A), D18.2 (A), D19.2 (A), FB4.2, R128.1, RV1.5, U4.6 (VDD), U9.2 (VI)

Notes on the sheet:
PA12 Col 3
Antenna connector
3.3V LDO
TX LED
Voice IC
PA10 Col 1
Combined volume pot. & ON/OFF Switch
Half-duplex TDD FM Transceiver
RF driver
Microcontroller
Audio amplifier
Charge LED
PA11 Col 2
DAN222-B common cathode internally connected to DAN222-A
Daughterboard
Flashlight LED
RF pre-driver
USB charge circuit
FM Receiver
Battery filtering and current limiting
LCD Connector
RX LED
PA3 Keypad Row 1 PA4 Keypad Row 2 PA5 Keypad Row 3 PA6 Keypad Row 4 PA10 Keypad Col 1 + EEPROM_SCL (opt: SPI0 CLK) PA11 Keypad Col 2 + EEPROM_SDA (opt: SPI0 MISO) PA12 Keypad Col 3 + VOICE_0 (opt: SPI0 MOSI) PA13 Keypad Col 4 + VOICE_1
Keypad backlight
EEPROM
Final RF amplifier
PA13 Col 4
